wyolum/pulse_v1/pulse_Images/DSCN9648.JPG

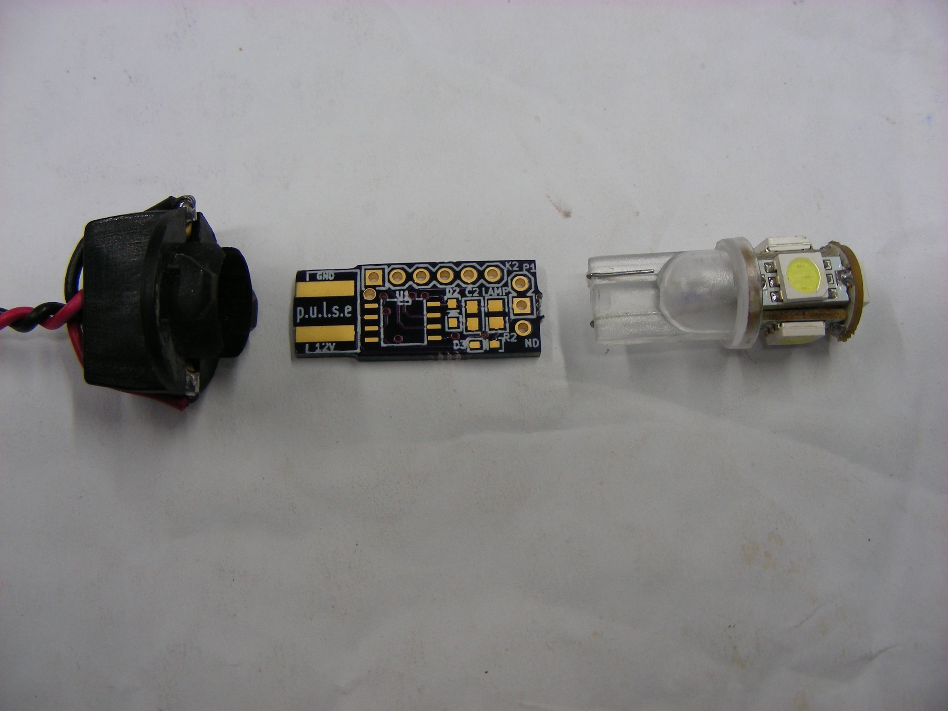
pulse_Images/DSCN9648.JPG
