wyolum/pulse_v1/pulse_Images/DSCN9651.JPG

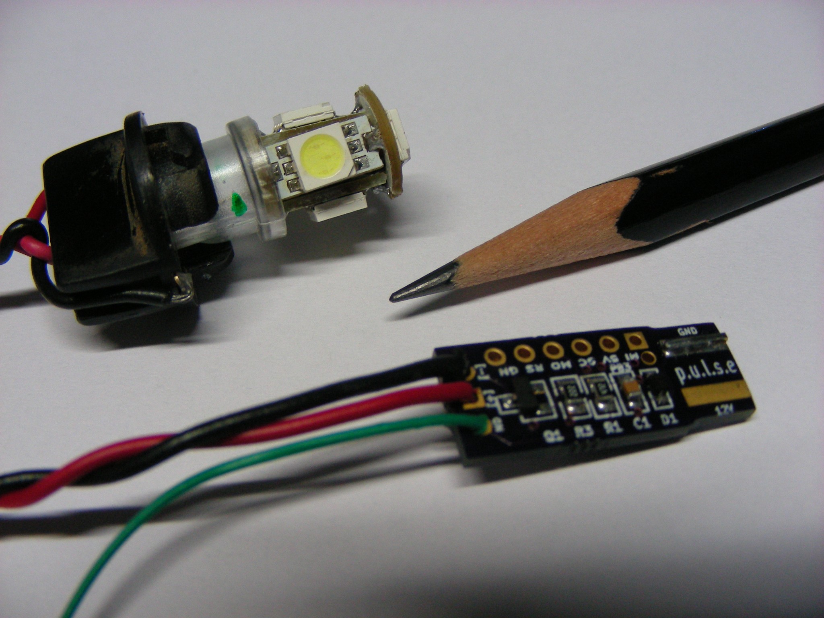
pulse_Images/DSCN9651.JPG
