wyolum/pulse_v1/pulse_Images/DSCN9652.JPG

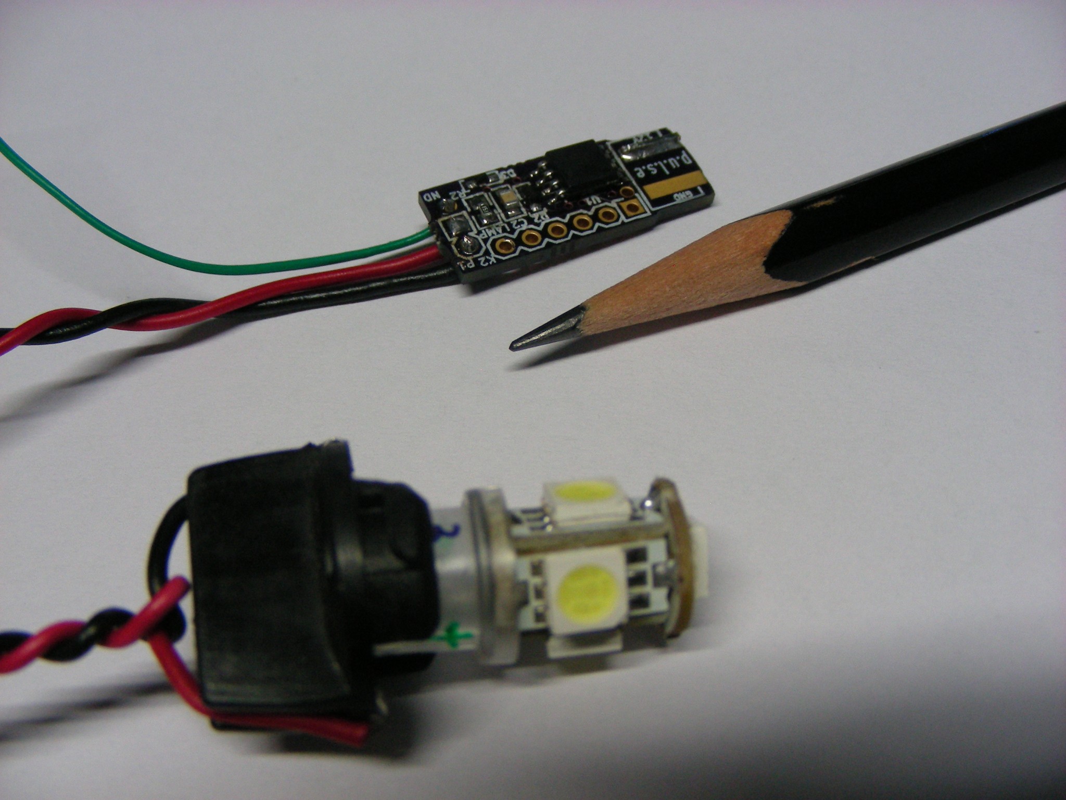
pulse_Images/DSCN9652.JPG
