wyolum/pulse_v1/pulse_Images/DSCN9653.JPG

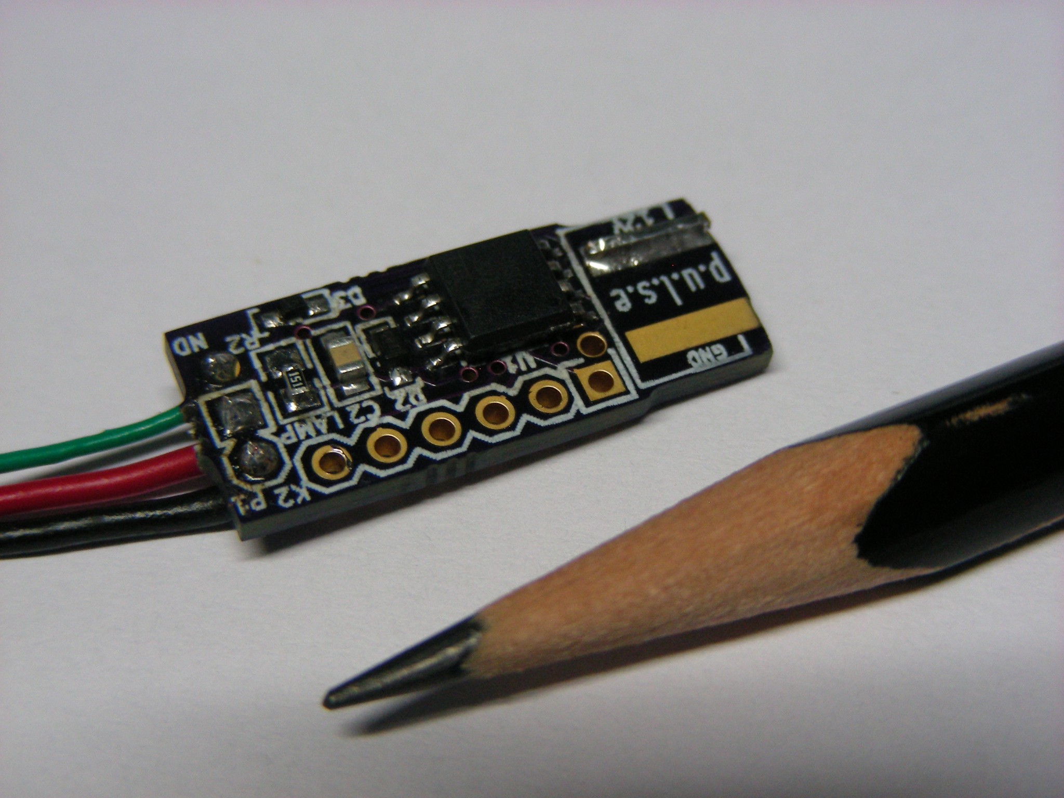
pulse_Images/DSCN9653.JPG
