wyolum/pulse_v1/pulse_Images/DSCN9654.JPG

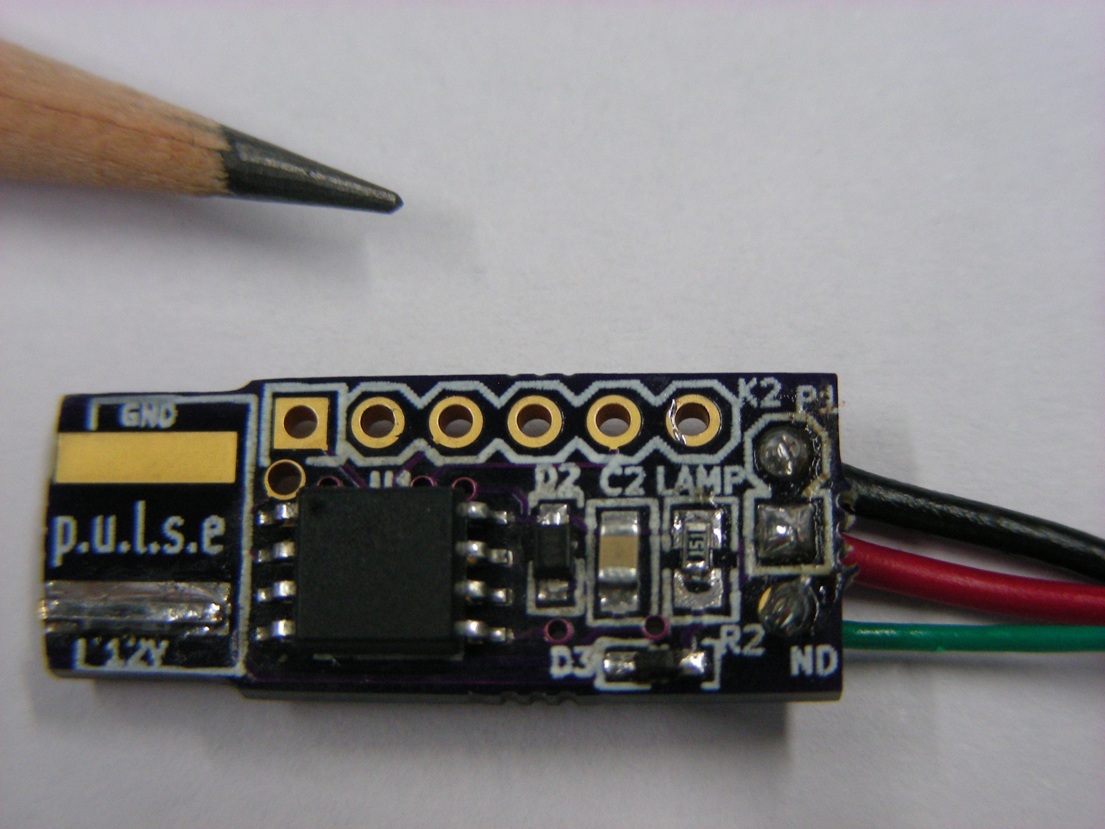
pulse_Images/DSCN9654.JPG
