wyolum/pulse_v1/pulse_Images/DSCN9655.JPG

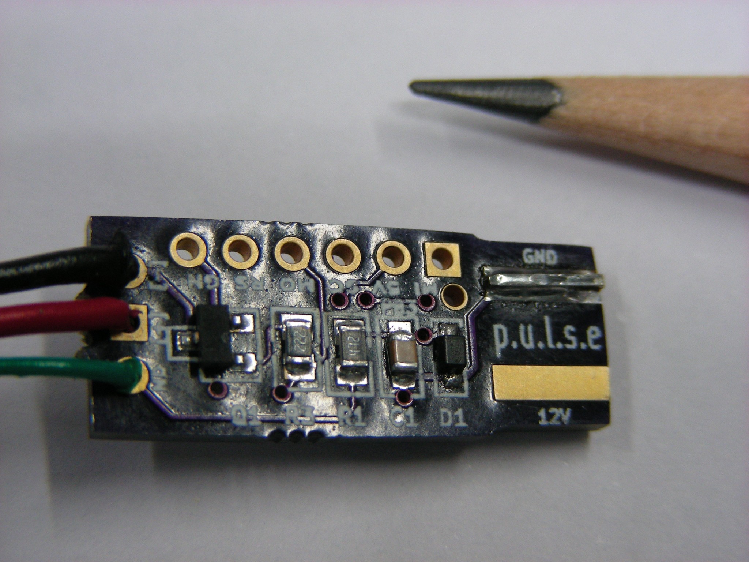
pulse_Images/DSCN9655.JPG
