wyolum/pulse_v1/pulse_Images/pulse_07.jpg

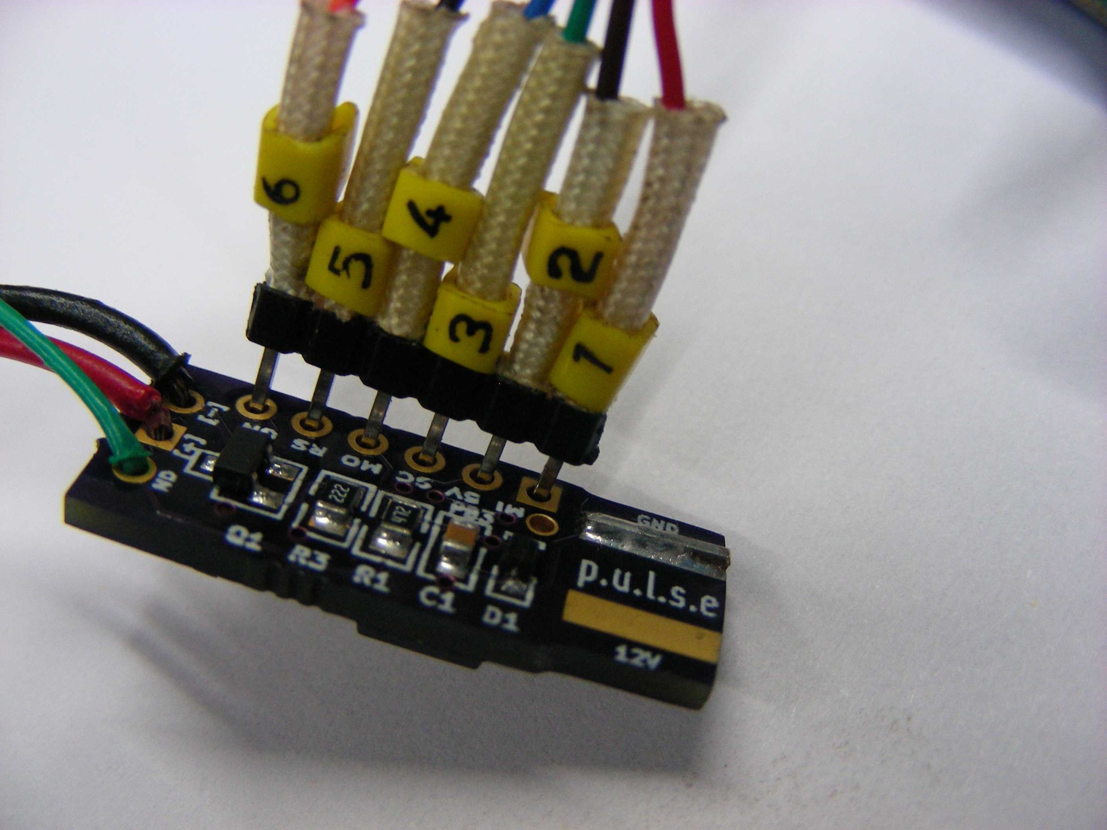
pulse_Images/pulse_07.jpg
